OliCar-del/tap-mania/tap-mania/Core/Inc/command_handler.h

/**
 ******************************************************************************
 * @file           : command_handler.h
 * @brief          : UART Command Processing
 ******************************************************************************
 */

#ifndef COMMAND_HANDLER_H
#define COMMAND_HANDLER_H

#include "main.h"
#include <stdint.h>

/**
 * @brief Process UART commands during gameplay
 */
void ProcessGameCommands(void);

#endif /* COMMAND_HANDLER_H */
